radiolok/fluidicpc/adder/adder_tb.v

module adder_tb();

parameter WIDTH=4;
parameter TEST_NUM=WIDTH*WIDTH;
reg clk;
reg [WIDTH-1:0] A;
reg [WIDTH-1:0] B;

wire [WIDTH-1:0] out;
wire co;
wire [WIDTH:0] res = {co, out};
reg [$clog2(TEST_NUM):0] test;
reg [$clog2(TEST_NUM):0] correct;

adder #(.WIDTH(WIDTH)) Adder(.A(A), .B(B), .out(out), .co(co), .ci(1'b0));

initial begin 
  $dumpfile("adder.vcd");
  $dumpvars(0, adder_tb);
  clk = 0;
  test = 0;
  correct = 0;
  A = $urandom();
  B = $urandom();
  forever #1 clk = ~clk;
end


wire[WIDTH:0] RC = A + B;

always @(clk) begin
  if (clk) begin
    test <= test + 1;
    if (test >= TEST_NUM) begin
      $display("TESTS: %d/%d", correct, test);
      if (test != correct) 
        $fatal();
      $finish();
    end
    if (res == RC) begin
      correct <= correct + 1;
    end
    else begin
      $display("%d: %d + %d: Got: %d, exp: %d", test, A, B, res, RC);
    end
  end
  else begin
      A <= $urandom();
      B <= $urandom();

  end
end

endmodule
